schusjon/rf_module_chain/module_filter_attenuator/rflego_pi_att.png

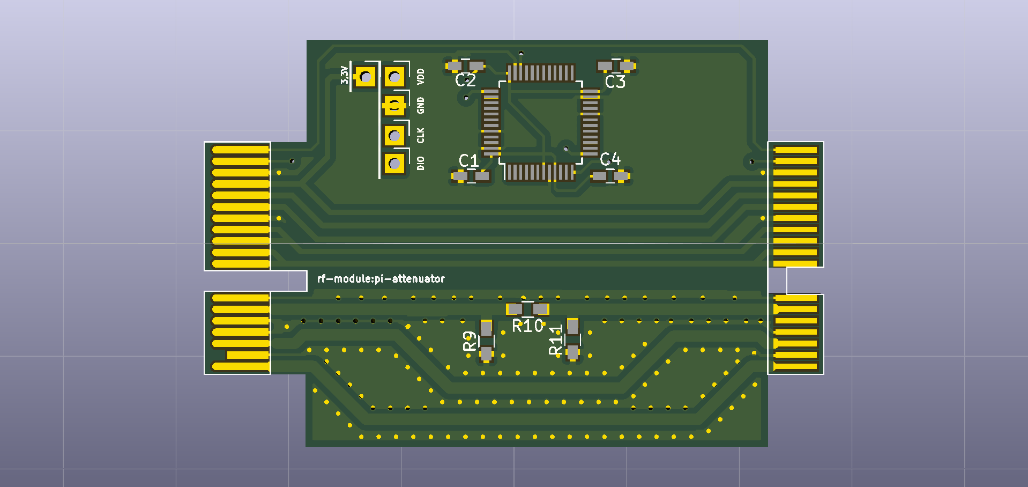
module_filter_attenuator/rflego_pi_att.png
