schusjon/rf_module_chain/module_start/rflego_mit_Bauteile.png

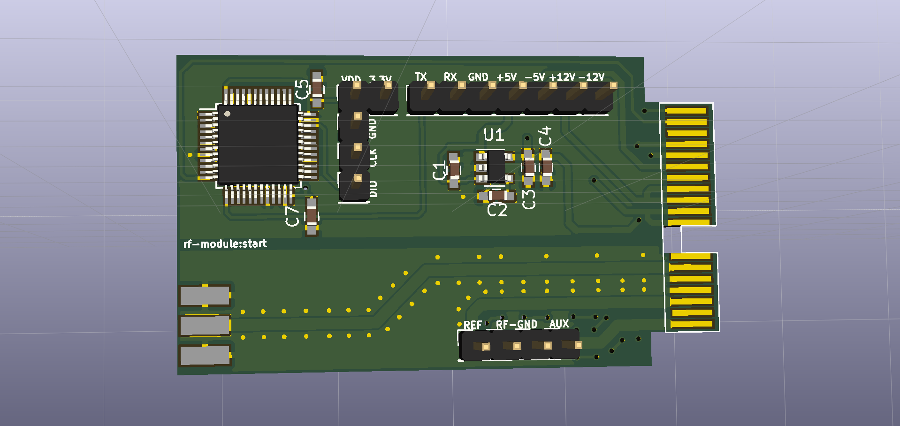
module_start/rflego_mit_Bauteile.png
