schusjon/rf_module_chain/module_termination/rflego_termination.png

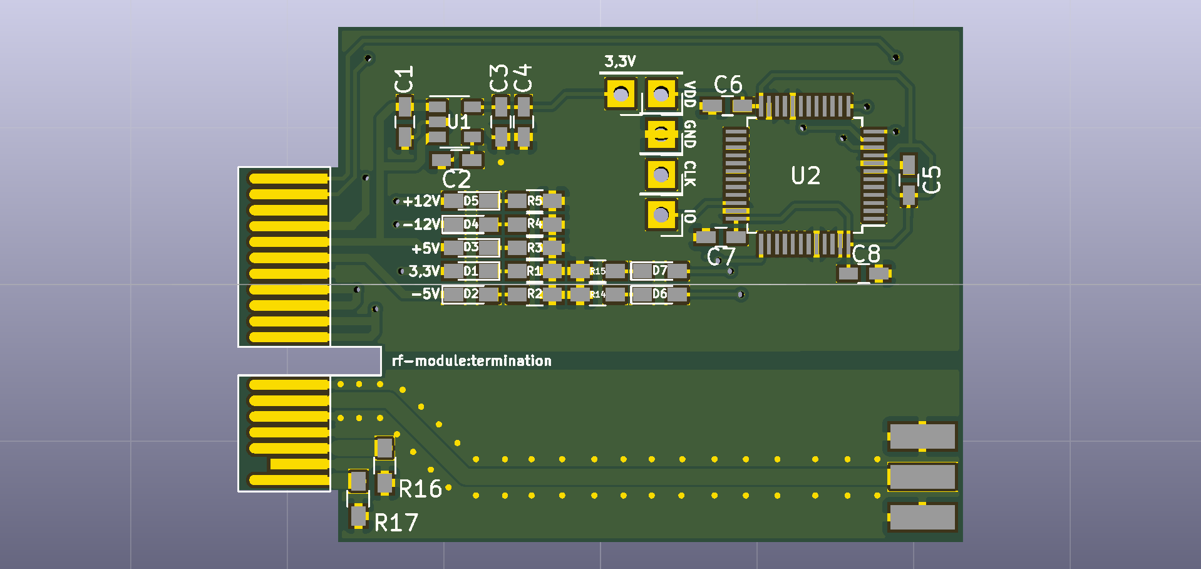
module_termination/rflego_termination.png
