schusjon/rf_module_chain/serial_communication/d4.jpg

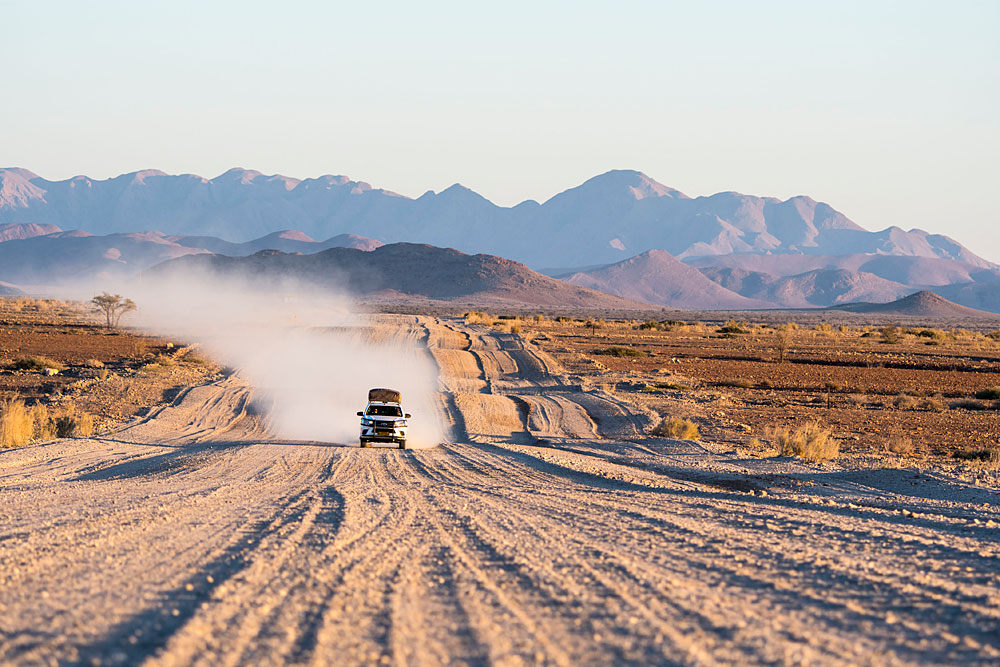
serial_communication/d4.jpg
