schusjon/rf_module_chain/serial_communication/d5.jpg

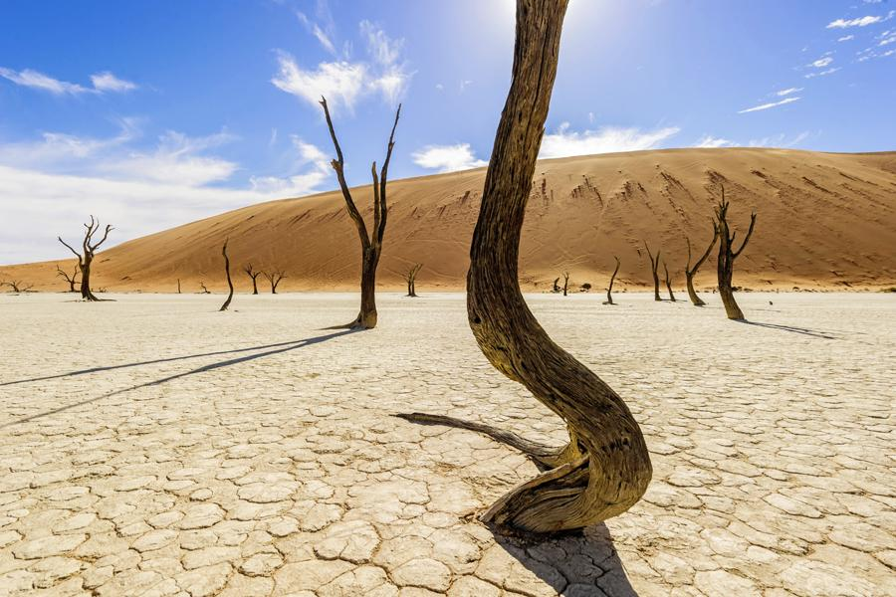
serial_communication/d5.jpg
