schusjon/rf_module_chain/serial_communication/d6.jpg

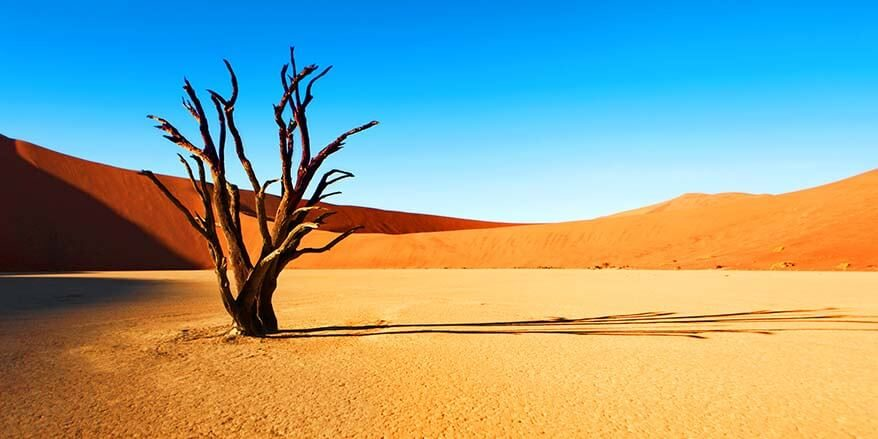
serial_communication/d6.jpg
