schusjon/rf_module_chain/serial_communication/main.cpp

#include "mainwindow.h"
#include <QApplication>
#include <iostream>

int main(int argc, char *argv[])
{
    QApplication a(argc, argv);
    MainWindow w;
    w.setWindowTitle("HF Lego Software");
    w.show();

    return a.exec();
}
